nilava/pixelbar/docs/preview/maptest.png

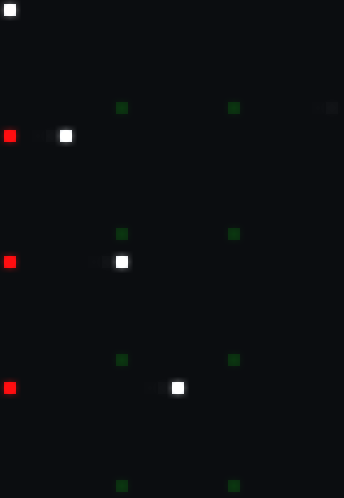
docs/preview/maptest.png
