nilava/pixelbar/docs/preview/rainbow.png

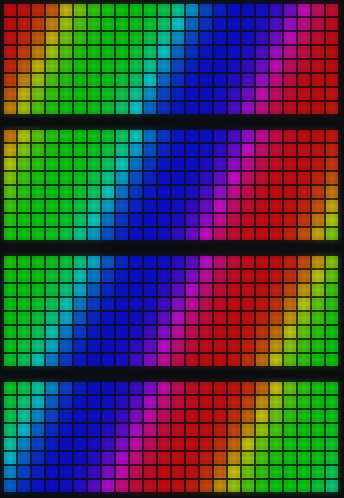
docs/preview/rainbow.png
