nilava/pixelbar/docs/preview/text.png

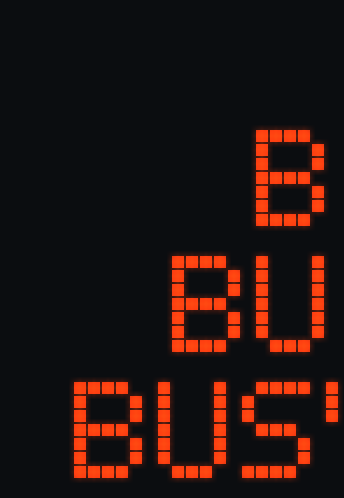
docs/preview/text.png
