nilava/pixelbar/docs/screens/clock.png

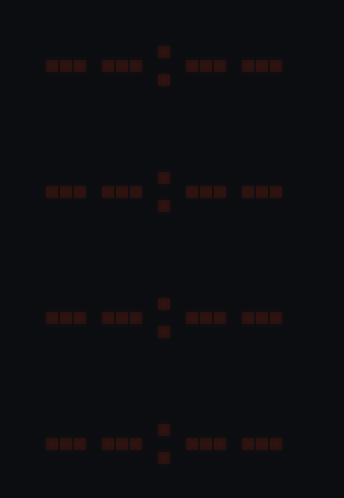
docs/screens/clock.png
