nilava/pixelbar/docs/screens/colorpick.png

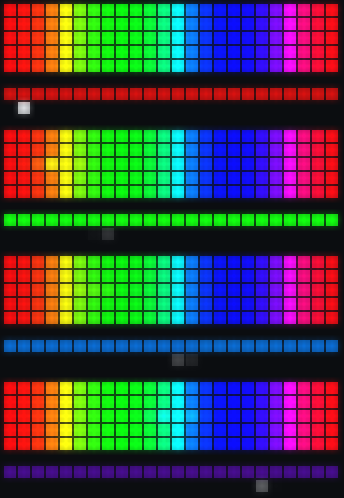
docs/screens/colorpick.png
