nilava/pixelbar/docs/screens/group.png

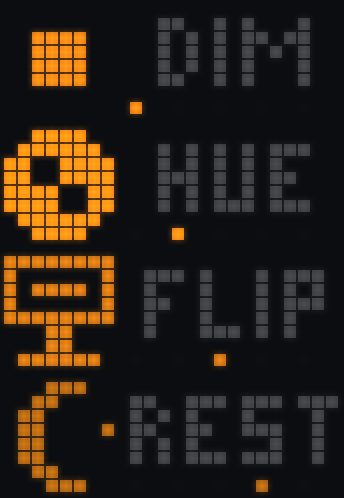
docs/screens/group.png
