nilava/pixelbar/docs/screens/scene.png

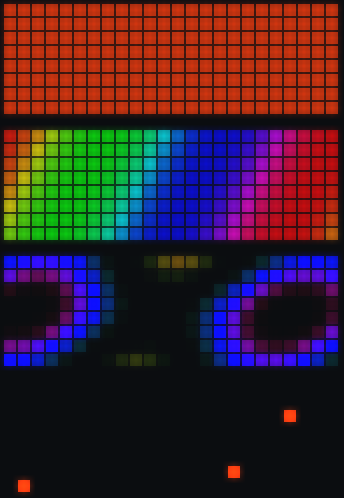
docs/screens/scene.png
