nilava/pixelbar/docs/screens/sleep.png

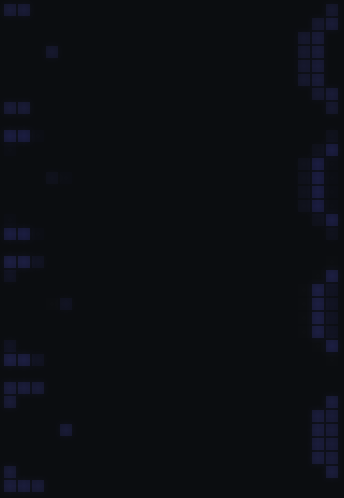
docs/screens/sleep.png
