nilava/pixelbar/docs/screens/statuspick.png

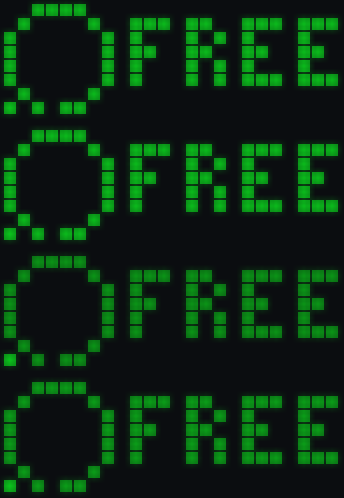
docs/screens/statuspick.png
