nilava/pixelbar/docs/screens/timer.png

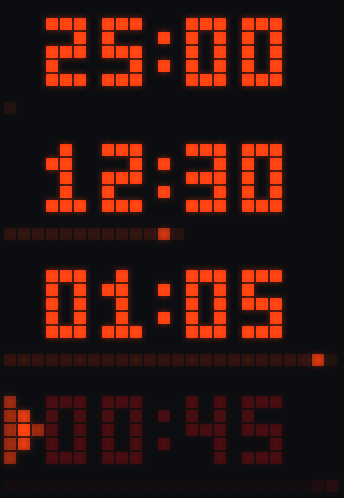
docs/screens/timer.png
