nilava/pixelbar/docs/screens/timerset.png

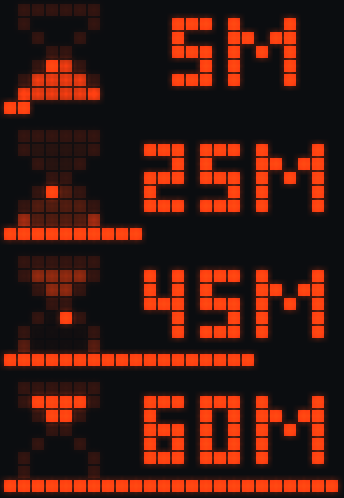
docs/screens/timerset.png
