nilava/pixelbar/docs/screens/wifiinfo.png

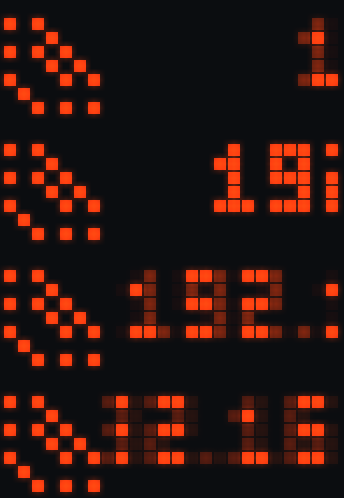
docs/screens/wifiinfo.png
