nilava/pixelbar/firmware/components/panel/src/icons.cpp

#include "panel/icons.h"

#include <cmath>

#include "panel/anim.h"
#include "panel/framebuffer.h"

namespace panel {
namespace {

// Eight binary digits per row, so the shape is readable in the source.
#define IR(a, b, c, d, e, f, g, h)                                            \
  static_cast<uint8_t>((a) << 7 | (b) << 6 | (c) << 5 | (d) << 4 | (e) << 3 | \
                       (f) << 2 | (g) << 1 | (h))

}  // namespace

const Icon kIconFree = {{
    IR(0,0,1,1,1,1,0,0),
    IR(0,1,0,0,0,0,1,0),
    IR(1,0,0,0,0,0,0,1),
    IR(1,0,0,0,0,0,0,1),
    IR(1,0,0,0,0,0,0,1),
    IR(1,0,0,0,0,0,0,1),
    IR(0,1,0,0,0,0,1,0),
    IR(0,0,1,1,1,1,0,0),
}};

const Icon kIconBusy = {{
    IR(0,0,1,1,1,1,0,0),
    IR(0,1,1,1,1,1,1,0),
    IR(1,1,1,1,1,1,1,1),
    IR(1,1,1,1,1,1,1,1),
    IR(1,1,1,1,1,1,1,1),
    IR(1,1,1,1,1,1,1,1),
    IR(0,1,1,1,1,1,1,0),
    IR(0,0,1,1,1,1,0,0),
}};

const Icon kIconDnd = {{
    IR(0,0,1,1,1,1,0,0),
    IR(0,1,0,0,0,0,1,0),
    IR(1,0,0,0,0,1,0,1),
    IR(1,0,0,0,1,0,0,1),
    IR(1,0,0,1,0,0,0,1),
    IR(1,0,1,0,0,0,0,1),
    IR(0,1,0,0,0,0,1,0),
    IR(0,0,1,1,1,1,0,0),
}};


// ------------------------------------------------------- the menu set
//
// One 8x8 glyph per top-level menu entry. Drawn to read at a glance from across
// a desk rather than to be admired up close: at this size a picture has about
// twenty lit pixels to make its point with, so each of these leans on one
// unmistakable silhouette instead of detail.

// A gear. Deliberately symmetric about both axes with eight teeth, so that
// rotating it through an eighth of a turn lands back on itself — which is what
// lets draw_sprite_rotated spin it forever without the shape appearing to
// wobble between frames.
const Icon kIconGear = {{
    IR(0,0,1,0,0,1,0,0),
    IR(0,1,1,1,1,1,1,0),
    IR(1,1,1,0,0,1,1,1),
    IR(0,1,0,0,0,0,1,0),
    IR(0,1,0,0,0,0,1,0),
    IR(1,1,1,0,0,1,1,1),
    IR(0,1,1,1,1,1,1,0),
    IR(0,0,1,0,0,1,0,0),
}};

// Four blocks: the shape everything uses for "a set of things".
const Icon kIconGrid = {{
    IR(0,0,0,0,0,0,0,0),
    IR(0,1,1,0,0,1,1,0),
    IR(0,1,1,0,0,1,1,0),
    IR(0,0,0,0,0,0,0,0),
    IR(0,0,0,0,0,0,0,0),
    IR(0,1,1,0,0,1,1,0),
    IR(0,1,1,0,0,1,1,0),
    IR(0,0,0,0,0,0,0,0),
}};

// A panel on a stand: the display settings.
const Icon kIconDisplay = {{
    IR(1,1,1,1,1,1,1,1),
    IR(1,0,0,0,0,0,0,1),
    IR(1,0,1,1,1,1,0,1),
    IR(1,0,0,0,0,0,0,1),
    IR(1,1,1,1,1,1,1,1),
    IR(0,0,0,1,1,0,0,0),
    IR(0,0,0,1,1,0,0,0),
    IR(0,1,1,1,1,1,1,0),
}};

// A hand: the touch settings.
const Icon kIconHand = {{
    IR(0,0,1,0,0,0,0,0),
    IR(0,1,1,1,0,1,0,0),
    IR(0,1,1,1,1,1,1,0),
    IR(0,1,1,1,1,1,1,0),
    IR(1,1,1,1,1,1,1,0),
    IR(1,1,1,1,1,1,1,0),
    IR(0,1,1,1,1,1,1,0),
    IR(0,0,1,1,1,1,0,0),
}};

// Waves radiating from a point: motion and gestures.
const Icon kIconMotion = {{
    IR(0,0,0,1,1,0,0,0),
    IR(0,0,1,0,0,1,0,0),
    IR(0,1,0,1,1,0,1,0),
    IR(1,0,1,0,0,1,0,1),
    IR(1,0,1,0,0,1,0,1),
    IR(0,1,0,1,1,0,1,0),
    IR(0,0,1,0,0,1,0,0),
    IR(0,0,0,1,1,0,0,0),
}};

// A padlock, for the lock screen and the touch lock.
const Icon kIconLock = {{
    IR(0,0,1,1,1,1,0,0),
    IR(0,1,1,0,0,1,1,0),
    IR(0,1,0,0,0,0,1,0),
    IR(1,1,1,1,1,1,1,1),
    IR(1,1,1,1,1,1,1,1),
    IR(1,1,1,0,0,1,1,1),
    IR(1,1,1,1,1,1,1,1),
    IR(1,1,1,1,1,1,1,1),
}};

// A cross, for anything that failed.
const Icon kIconCross = {{
    IR(0,0,0,0,0,0,0,0),
    IR(0,1,1,0,0,1,1,0),
    IR(0,1,1,1,1,1,1,0),
    IR(0,0,1,1,1,1,0,0),
    IR(0,0,1,1,1,1,0,0),
    IR(0,1,1,1,1,1,1,0),
    IR(0,1,1,0,0,1,1,0),
    IR(0,0,0,0,0,0,0,0),
}};

// An exclamation inside a triangle: a warning.
const Icon kIconWarning = {{
    IR(0,0,0,1,1,0,0,0),
    IR(0,0,0,1,1,0,0,0),
    IR(0,0,1,1,1,1,0,0),
    IR(0,0,1,0,0,1,0,0),
    IR(0,1,1,0,0,1,1,0),
    IR(0,1,1,1,1,1,1,0),
    IR(1,1,1,0,0,1,1,1),
    IR(1,1,1,1,1,1,1,1),
}};

// An arrow into a tray: an update arriving.
const Icon kIconDownload = {{
    IR(0,0,0,1,1,0,0,0),
    IR(0,0,0,1,1,0,0,0),
    IR(0,0,0,1,1,0,0,0),
    IR(1,1,0,1,1,0,1,1),
    IR(0,1,1,1,1,1,1,0),
    IR(0,0,1,1,1,1,0,0),
    IR(0,0,0,1,1,0,0,0),
    IR(1,1,1,1,1,1,1,1),
}};

// Four blocks of colour. Drawn flat and coloured at the call site like every
// other icon, so on the menu row it takes the entry's own colour.
const Icon kIconPalette = {{
    IR(0,0,1,1,1,1,0,0),
    IR(0,1,1,1,1,1,1,0),
    IR(1,1,0,0,1,1,1,1),
    IR(1,1,0,0,1,1,1,1),
    IR(1,1,1,1,0,0,1,1),
    IR(1,1,1,1,0,0,1,1),
    IR(0,1,1,1,1,1,1,0),
    IR(0,0,1,1,1,1,0,0),
}};

// A lower-case i in a ring: about.
const Icon kIconInfo = {{
    IR(0,0,1,1,1,1,0,0),
    IR(0,1,0,0,0,0,1,0),
    IR(1,0,0,1,1,0,0,1),
    IR(1,0,0,0,0,0,0,1),
    IR(1,0,0,1,1,0,0,1),
    IR(1,0,0,1,1,0,0,1),
    IR(0,1,0,1,1,0,1,0),
    IR(0,0,1,1,1,1,0,0),
}};

namespace {
// The handset never touches rows 1 and 2, which is where the ripples live.
const Icon kCallFrames[4] = {
    {{IR(0,0,0,0,0,0,0,0), IR(0,0,0,0,0,0,0,0), IR(0,0,0,0,0,0,0,0),
      IR(1,1,0,0,0,0,1,1), IR(1,1,0,0,0,0,1,1), IR(0,1,0,0,0,0,1,0),
      IR(0,0,1,1,1,1,0,0), IR(0,0,0,0,0,0,0,0)}},
    {{IR(0,0,0,0,0,0,0,0), IR(0,0,0,0,0,0,0,0), IR(0,1,0,0,0,0,1,0),
      IR(1,1,0,0,0,0,1,1), IR(1,1,0,0,0,0,1,1), IR(0,1,0,0,0,0,1,0),
      IR(0,0,1,1,1,1,0,0), IR(0,0,0,0,0,0,0,0)}},
    {{IR(0,0,0,0,0,0,0,0), IR(1,0,0,0,0,0,0,1), IR(0,1,0,0,0,0,1,0),
      IR(1,1,0,0,0,0,1,1), IR(1,1,0,0,0,0,1,1), IR(0,1,0,0,0,0,1,0),
      IR(0,0,1,1,1,1,0,0), IR(0,0,0,0,0,0,0,0)}},
    {{IR(0,0,0,0,0,0,0,0), IR(1,0,0,0,0,0,0,1), IR(0,0,0,0,0,0,0,0),
      IR(1,1,0,0,0,0,1,1), IR(1,1,0,0,0,0,1,1), IR(0,1,0,0,0,0,1,0),
      IR(0,0,1,1,1,1,0,0), IR(0,0,0,0,0,0,0,0)}},
};
}  // namespace
const AnimIcon kAnimCall = {kCallFrames, 4, 8.0f, false};

const Icon kIconMoon = {{
    IR(0,0,0,1,1,1,0,0),
    IR(0,0,1,1,0,0,0,0),
    IR(0,1,1,0,0,0,0,0),
    IR(0,1,1,0,0,0,0,1),
    IR(0,1,1,0,0,0,0,0),
    IR(0,1,1,0,0,0,0,0),
    IR(0,0,1,1,0,0,0,0),
    IR(0,0,0,1,1,1,0,0),
}};

const Icon kIconSunCore = {{
    IR(0,0,0,0,0,0,0,0),
    IR(0,0,0,0,0,0,0,0),
    IR(0,0,1,1,1,1,0,0),
    IR(0,0,1,1,1,1,0,0),
    IR(0,0,1,1,1,1,0,0),
    IR(0,0,1,1,1,1,0,0),
    IR(0,0,0,0,0,0,0,0),
    IR(0,0,0,0,0,0,0,0),
}};

const Icon kIconSunRays = {{
    IR(0,0,0,1,1,0,0,0),
    IR(0,1,0,0,0,0,1,0),
    IR(0,0,0,0,0,0,0,0),
    IR(1,0,0,0,0,0,0,1),
    IR(1,0,0,0,0,0,0,1),
    IR(0,0,0,0,0,0,0,0),
    IR(0,1,0,0,0,0,1,0),
    IR(0,0,0,1,1,0,0,0),
}};

const Icon kIconHourglass = {{
    IR(0,1,1,1,1,1,1,0),
    IR(0,1,0,0,0,0,1,0),
    IR(0,0,1,0,0,1,0,0),
    IR(0,0,0,1,1,0,0,0),
    IR(0,0,1,0,0,1,0,0),
    IR(0,1,0,0,0,0,1,0),
    IR(0,1,0,0,0,0,1,0),
    IR(0,1,1,1,1,1,1,0),
}};

const Icon kIconHourglassTop = {{
    IR(0,0,0,0,0,0,0,0),
    IR(0,0,1,1,1,1,0,0),
    IR(0,0,0,1,1,0,0,0),
    IR(0,0,0,0,0,0,0,0),
    IR(0,0,0,0,0,0,0,0),
    IR(0,0,0,0,0,0,0,0),
    IR(0,0,0,0,0,0,0,0),
    IR(0,0,0,0,0,0,0,0),
}};

const Icon kIconHourglassBottom = {{
    IR(0,0,0,0,0,0,0,0),
    IR(0,0,0,0,0,0,0,0),
    IR(0,0,0,0,0,0,0,0),
    IR(0,0,0,0,0,0,0,0),
    IR(0,0,0,1,1,0,0,0),
    IR(0,0,1,1,1,1,0,0),
    IR(0,1,1,1,1,1,1,0),
    IR(0,0,0,0,0,0,0,0),
}};

namespace {
// Each frame lights one more arc than the last, so it reads as filling.
const Icon kWifiFrames[5] = {
    {{IR(0,0,0,0,0,0,0,0), IR(0,0,0,0,0,0,0,0), IR(0,0,0,0,0,0,0,0),
      IR(0,0,0,0,0,0,0,0), IR(0,0,0,0,0,0,0,0), IR(0,0,0,0,0,0,0,0),
      IR(0,0,0,1,1,0,0,0), IR(0,0,0,1,1,0,0,0)}},
    {{IR(0,0,0,0,0,0,0,0), IR(0,0,0,0,0,0,0,0), IR(0,0,0,0,0,0,0,0),
      IR(0,0,0,0,0,0,0,0), IR(0,0,0,1,1,0,0,0), IR(0,0,0,0,0,0,0,0),
      IR(0,0,0,1,1,0,0,0), IR(0,0,0,1,1,0,0,0)}},
    {{IR(0,0,0,0,0,0,0,0), IR(0,0,0,0,0,0,0,0), IR(0,0,1,1,1,1,0,0),
      IR(0,1,0,0,0,0,1,0), IR(0,0,0,1,1,0,0,0), IR(0,0,0,0,0,0,0,0),
      IR(0,0,0,1,1,0,0,0), IR(0,0,0,1,1,0,0,0)}},
    {{IR(0,1,1,1,1,1,1,0), IR(1,0,0,0,0,0,0,1), IR(0,0,1,1,1,1,0,0),
      IR(0,1,0,0,0,0,1,0), IR(0,0,0,1,1,0,0,0), IR(0,0,0,0,0,0,0,0),
      IR(0,0,0,1,1,0,0,0), IR(0,0,0,1,1,0,0,0)}},
    {{IR(0,1,1,1,1,1,1,0), IR(1,0,0,0,0,0,0,1), IR(0,0,1,1,1,1,0,0),
      IR(0,1,0,0,0,0,1,0), IR(0,0,0,1,1,0,0,0), IR(0,0,0,0,0,0,0,0),
      IR(0,0,0,1,1,0,0,0), IR(0,0,0,1,1,0,0,0)}},
};
// Short arm first, then up the long one, so it draws like a pen stroke.
const uint8_t kCheckPts[] = {0x13, 0x24, 0x35, 0x44, 0x53, 0x62, 0x71};
}  // namespace
const AnimIcon kAnimWifi = {kWifiFrames, 5, 4.0f, false};
const StrokeIcon kStrokeCheck = {kCheckPts, sizeof(kCheckPts)};

#undef IR

// ---------------------------------------------------------------- drawing

void draw_icon(Framebuffer& fb, int x, int y, const Icon& ic, RGB color) {
  for (int row = 0; row < kIconH; ++row) {
    for (int col = 0; col < kIconW; ++col) {
      if (ic.rows[row] & (1 << (kIconW - 1 - col))) fb.set(x + col, y + row, color);
    }
  }
}

void draw_icon_aa(Framebuffer& fb, float x, float y, const Icon& ic, RGB color) {
  for (int row = 0; row < kIconH; ++row) {
    for (int col = 0; col < kIconW; ++col) {
      if (ic.rows[row] & (1 << (kIconW - 1 - col))) {
        fb.set_aa2(x + col, y + row, color, 1.0f, Blend::Add);
      }
    }
  }
}

int icon_lit_count(const Icon& ic) {
  int n = 0;
  for (int row = 0; row < kIconH; ++row) {
    for (int col = 0; col < kIconW; ++col) {
      if (ic.rows[row] & (1 << (kIconW - 1 - col))) ++n;
    }
  }
  return n;
}

const Icon& anim_frame(const AnimIcon& a, double t_s) {
  if (a.count == 0) return a.frames[0];
  double steps = t_s * a.fps;
  if (steps < 0) steps = 0;
  long i = static_cast<long>(steps);
  if (a.ping_pong && a.count > 1) {
    const long span = 2 * a.count - 2;
    long p = i % span;
    if (p < 0) p += span;
    if (p >= a.count) p = span - p;
    return a.frames[p];
  }
  return a.frames[i % a.count];
}

void draw_anim_icon(Framebuffer& fb, int x, int y, const AnimIcon& a, double t_s, RGB color) {
  draw_icon(fb, x, y, anim_frame(a, t_s), color);
}

void draw_icon_masked(Framebuffer& fb, int x, int y, const Icon& shell, const Icon& fill,
                      float fraction, RGB shell_c, RGB fill_c) {
  draw_icon(fb, x, y, shell, shell_c);
  const float level = clamp01(fraction) * kIconH;  // rows lit from the bottom
  for (int row = 0; row < kIconH; ++row) {
    const int from_bottom = kIconH - 1 - row;
    float cov = level - from_bottom;
    if (cov <= 0.0f) continue;
    if (cov > 1.0f) cov = 1.0f;
    for (int col = 0; col < kIconW; ++col) {
      if (fill.rows[row] & (1 << (kIconW - 1 - col))) {
        fb.blend(x + col, y + row, fill_c, cov);
      }
    }
  }
}

void draw_stroke_icon(Framebuffer& fb, int x, int y, const StrokeIcon& s, float progress,
                      RGB body, RGB tip) {
  const float p = clamp01(progress) * s.n;
  const int full = static_cast<int>(p);
  for (int i = 0; i < s.n && i <= full; ++i) {
    const int px = (s.pts[i] >> 4) & 0xF;
    const int py = s.pts[i] & 0xF;
    if (i == full) {
      fb.blend(x + px, y + py, tip, p - full);  // the leading point fades in
    } else {
      fb.set(x + px, y + py, body);
    }
  }
}

void draw_hourglass(Framebuffer& fb, int x, int y, float remaining, double t_s,
                    RGB shell, RGB sand) {
  draw_icon(fb, x, y, kIconHourglass, shell);
  // Sand left in the top chamber, sand collected in the bottom.
  const float r = clamp01(remaining);
  for (int row = 0; row < kIconH; ++row) {
    for (int col = 0; col < kIconW; ++col) {
      if (kIconHourglassTop.rows[row] & (1 << (kIconW - 1 - col))) {
        fb.blend(x + col, y + row, sand, r);
      }
      if (kIconHourglassBottom.rows[row] & (1 << (kIconW - 1 - col))) {
        fb.blend(x + col, y + row, sand, 1.0f - r);
      }
    }
  }
  // One grain in transit, so it reads as running rather than paused.
  if (r > 0.0f && r < 1.0f) {
    const int gx = (static_cast<int>(t_s * 2.0) & 1) ? 4 : 3;
    fb.set(x + gx, y + 4, sand);
  }
}

}  // namespace panel
